89Mods/z80-llm/Z80/crc32c.c

#include <stdint.h>
#include "crc32c.h"

// Tables for CRC word-wise calculation, definitions of LONG and SHORT, and CRC
// shifts by LONG and SHORT bytes.
#include "crc32c.h"


// Table for a 64-bits-at-a-time software CRC-32C calculation. This table
// has built into it the pre and post bit inversion of the CRC.
const uint32_t crc32c_table[256*8] = {
   0x527d5351, 0xa016d052, 0xb34623a6, 0x412da0a5, 0x95e7c44e, 0x678c474d,
    0x74dcb4b9, 0x86b737ba, 0xd8a40b9e, 0x2acf889d, 0x399f7b69, 0xcbf4f86a,
    0x1f3e9c81, 0xed551f82, 0xfe05ec76, 0x0c6e6f75, 0x4223943e, 0xb048173d,
    0xa318e4c9, 0x517367ca, 0x85b90321, 0x77d28022, 0x648273d6, 0x96e9f0d5,
    0xc8faccf1, 0x3a914ff2, 0x29c1bc06, 0xdbaa3f05, 0x0f605bee, 0xfd0bd8ed,
    0xee5b2b19, 0x1c30a81a, 0x72c0dd8f, 0x80ab5e8c, 0x93fbad78, 0x61902e7b,
    0xb55a4a90, 0x4731c993, 0x54613a67, 0xa60ab964, 0xf8198540, 0x0a720643,
    0x1922f5b7, 0xeb4976b4, 0x3f83125f, 0xcde8915c, 0xdeb862a8, 0x2cd3e1ab,
    0x629e1ae0, 0x90f599e3, 0x83a56a17, 0x71cee914, 0xa5048dff, 0x576f0efc,
    0x443ffd08, 0xb6547e0b, 0xe847422f, 0x1a2cc12c, 0x097c32d8, 0xfb17b1db,
    0x2fddd530, 0xddb65633, 0xcee6a5c7, 0x3c8d26c4, 0x13064eed, 0xe16dcdee,
    0xf23d3e1a, 0x0056bd19, 0xd49cd9f2, 0x26f75af1, 0x35a7a905, 0xc7cc2a06,
    0x99df1622, 0x6bb49521, 0x78e466d5, 0x8a8fe5d6, 0x5e45813d, 0xac2e023e,
    0xbf7ef1ca, 0x4d1572c9, 0x03588982, 0xf1330a81, 0xe263f975, 0x10087a76,
    0xc4c21e9d, 0x36a99d9e, 0x25f96e6a, 0xd792ed69, 0x8981d14d, 0x7bea524e,
    0x68baa1ba, 0x9ad122b9, 0x4e1b4652, 0xbc70c551, 0xaf2036a5, 0x5d4bb5a6,
    0x33bbc033, 0xc1d04330, 0xd280b0c4, 0x20eb33c7, 0xf421572c, 0x064ad42f,
    0x151a27db, 0xe771a4d8, 0xb96298fc, 0x4b091bff, 0x5859e80b, 0xaa326b08,
    0x7ef80fe3, 0x8c938ce0, 0x9fc37f14, 0x6da8fc17, 0x23e5075c, 0xd18e845f,
    0xc2de77ab, 0x30b5f4a8, 0xe47f9043, 0x16141340, 0x0544e0b4, 0xf72f63b7,
    0xa93c5f93, 0x5b57dc90, 0x48072f64, 0xba6cac67, 0x6ea6c88c, 0x9ccd4b8f,
    0x8f9db87b, 0x7df63b78, 0xd08b6829, 0x22e0eb2a, 0x31b018de, 0xc3db9bdd,
    0x1711ff36, 0xe57a7c35, 0xf62a8fc1, 0x04410cc2, 0x5a5230e6, 0xa839b3e5,
    0xbb694011, 0x4902c312, 0x9dc8a7f9, 0x6fa324fa, 0x7cf3d70e, 0x8e98540d,
    0xc0d5af46, 0x32be2c45, 0x21eedfb1, 0xd3855cb2, 0x074f3859, 0xf524bb5a,
    0xe67448ae, 0x141fcbad, 0x4a0cf789, 0xb867748a, 0xab37877e, 0x595c047d,
    0x8d966096, 0x7ffde395, 0x6cad1061, 0x9ec69362, 0xf036e6f7, 0x025d65f4,
    0x110d9600, 0xe3661503, 0x37ac71e8, 0xc5c7f2eb, 0xd697011f, 0x24fc821c,
    0x7aefbe38, 0x88843d3b, 0x9bd4cecf, 0x69bf4dcc, 0xbd752927, 0x4f1eaa24,
    0x5c4e59d0, 0xae25dad3, 0xe0682198, 0x1203a29b, 0x0153516f, 0xf338d26c,
    0x27f2b687, 0xd5993584, 0xc6c9c670, 0x34a24573, 0x6ab17957, 0x98dafa54,
    0x8b8a09a0, 0x79e18aa3, 0xad2bee48, 0x5f406d4b, 0x4c109ebf, 0xbe7b1dbc,
    0x91f07595, 0x639bf696, 0x70cb0562, 0x82a08661, 0x566ae28a, 0xa4016189,
    0xb751927d, 0x453a117e, 0x1b292d5a, 0xe942ae59, 0xfa125dad, 0x0879deae,
    0xdcb3ba45, 0x2ed83946, 0x3d88cab2, 0xcfe349b1, 0x81aeb2fa, 0x73c531f9,
    0x6095c20d, 0x92fe410e, 0x463425e5, 0xb45fa6e6, 0xa70f5512, 0x5564d611,
    0x0b77ea35, 0xf91c6936, 0xea4c9ac2, 0x182719c1, 0xcced7d2a, 0x3e86fe29,
    0x2dd60ddd, 0xdfbd8ede, 0xb14dfb4b, 0x43267848, 0x50768bbc, 0xa21d08bf,
    0x76d76c54, 0x84bcef57, 0x97ec1ca3, 0x65879fa0, 0x3b94a384, 0xc9ff2087,
    0xdaafd373, 0x28c45070, 0xfc0e349b, 0x0e65b798, 0x1d35446c, 0xef5ec76f,
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
};

// Table-driven software version as a fall-back. This is about 15 times slower
// than using the hardware instructions. This assumes little-endian integers,
// as is the case on Intel processors that the assembler code here is for.
uint32_t crc32c_sw(uint32_t crc, const uint8_t *data, uint32_t len) {
    if (!data) return 0;
    int aaa = 8;
    while (len && aaa != 0) {
        crc = (crc >> 8) ^ crc32c_table[(crc ^ *data++) & 0xff];
        len--;
        aaa--;
    }
    uint32_t n = len >> 3;
    for (uint32_t i = 0; i < n; i++) {
        uint64_t word = crc ^ ((uint64_t const *)data)[i];
        crc = crc32c_table[7*256 + (word & 0xff)] ^
              crc32c_table[6*256 + ((word >> 8) & 0xff)] ^
              crc32c_table[5*256 + ((word >> 16) & 0xff)] ^
              crc32c_table[4*256 + ((word >> 24) & 0xff)] ^
              crc32c_table[3*256 + ((word >> 32) & 0xff)] ^
              crc32c_table[2*256 + ((word >> 40) & 0xff)] ^
              crc32c_table[1*256 + ((word >> 48) & 0xff)] ^
              crc32c_table[0*256 + (word >> 56)];
    }
    data += n << 3;
    len &= 7;
    while (len) {
        len--;
        crc = (crc >> 8) ^ crc32c_table[(crc ^ *data++) & 0xff];
    }
    return crc;
}

/* crc32c.c -- compute CRC-32C
 * Copyright (C) 2013, 2021, 2023 Mark Adler
 * Version 1.3  7 Dec 2023  Mark Adler
 */

/*
  This software is provided 'as-is', without any express or implied
  warranty. In no event will the author be held liable for any damages
  arising from the use of this software.

  Permission is granted to anyone to use this software for any purpose,
  including commercial applications, and to alter it and redistribute it
  freely, subject to the following restrictions:

  1. The origin of this software must not be misrepresented; you must not
     claim that you wrote the original software. If you use this software
     in a product, an acknowledgment in the product documentation would be
     appreciated but is not required.
  2. Altered source versions must be plainly marked as such, and must not be
     misrepresented as being the original software.
  3. This notice may not be removed or altered from any source distribution.

  Mark Adler
  madler@alumni.caltech.edu
 */
